MZandtheRaspberryPi/prod_disaster_counter/rev2/arduino_prod_disaster_counter_rev2/pin_mapping.h

#ifndef PIN_MAPPING_H
#define PIN_MAPPING_H

#include <Arduino.h>

namespace pin_mapping 
{
  
// pin mapping
const int BUTTON_PIN = PB4;
const int LED_PIN = PB1;

} // end namespace pin_mapping

#endif
